marsairforce/ibanez_rg350ex/photos/IMG_4963.jpg

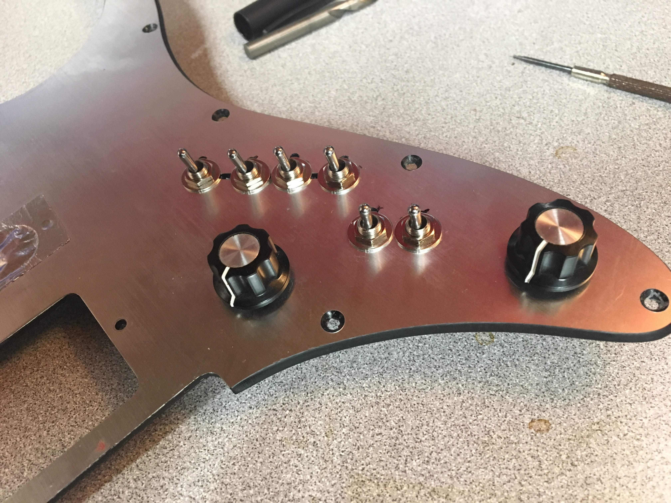
photos/IMG_4963.jpg
