marsairforce/ibanez_rg350ex/photos/IMG_4964.jpg

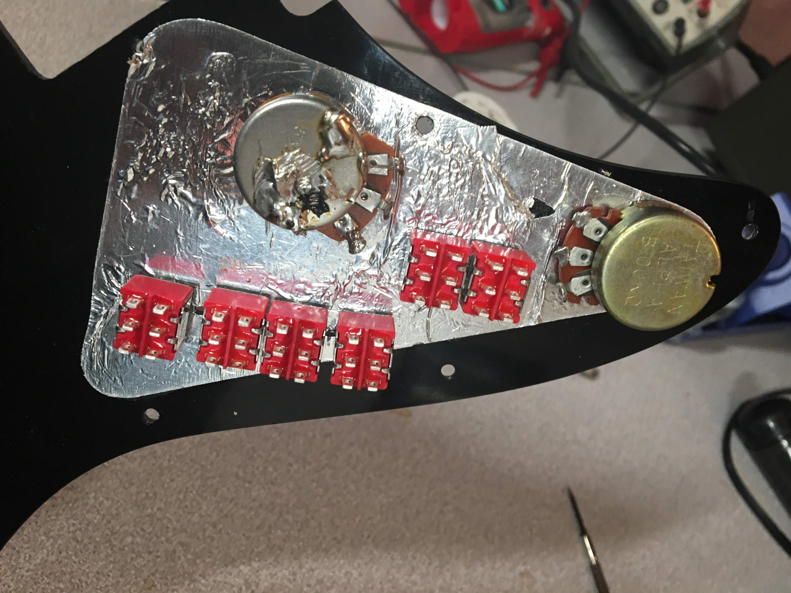
photos/IMG_4964.jpg
