marsairforce/ibanez_rg350ex/photos/IMG_4965.jpg

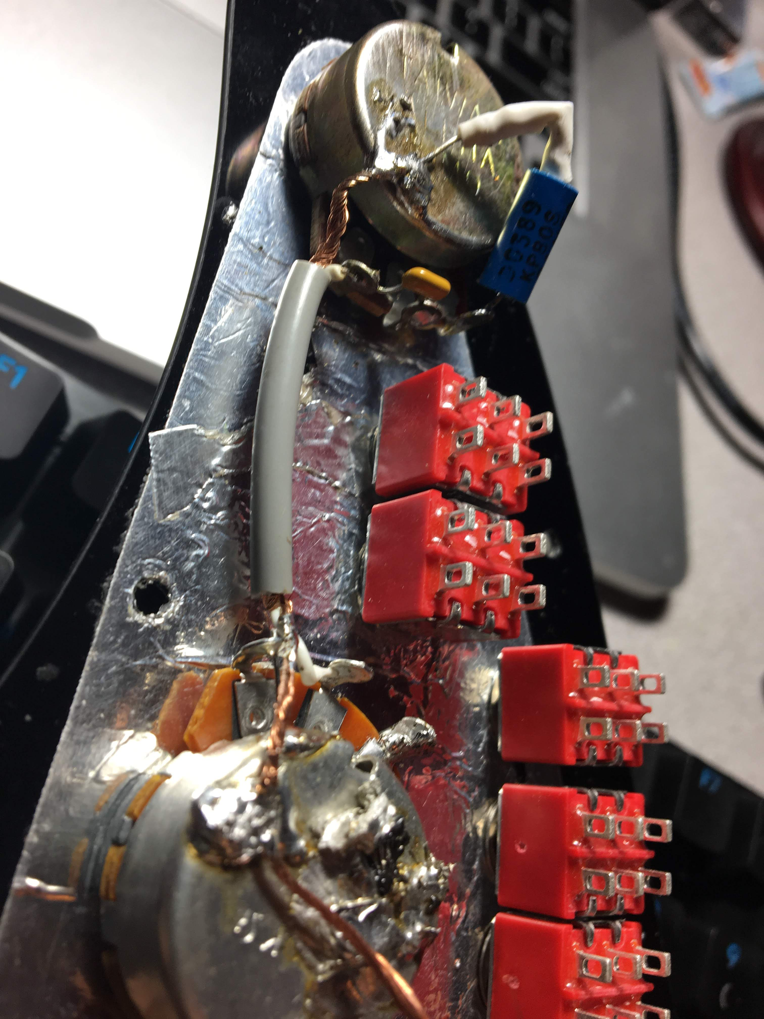
photos/IMG_4965.jpg
