marsairforce/ibanez_rg350ex/photos/IMG_4967.jpg

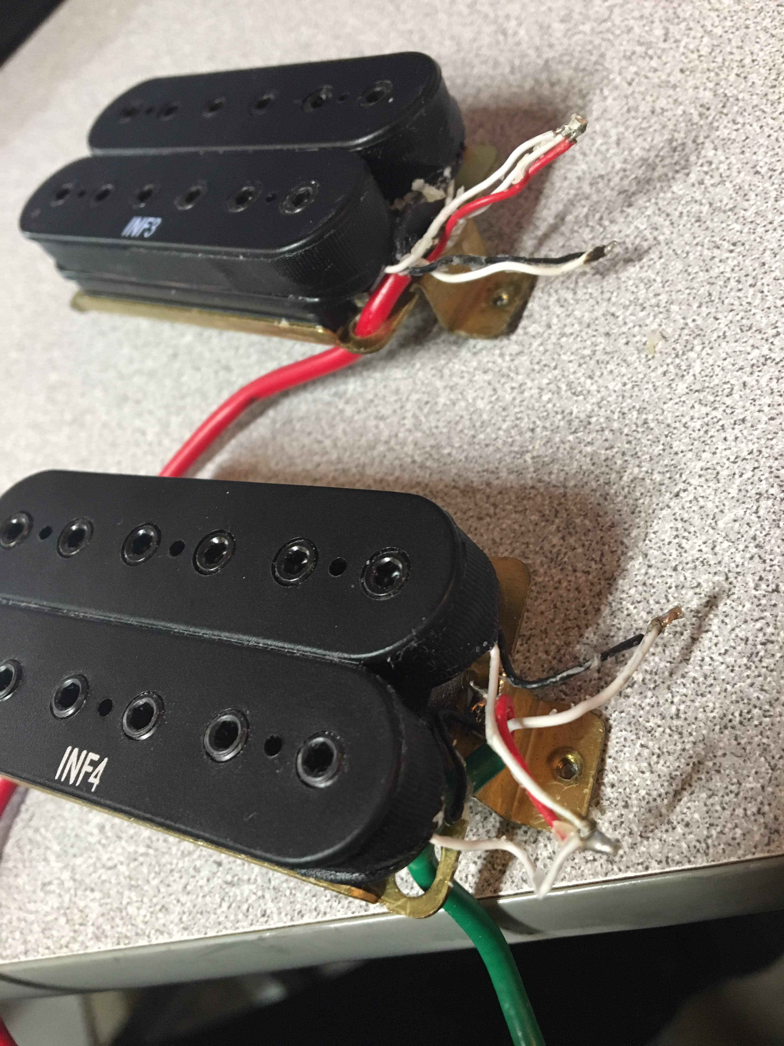
photos/IMG_4967.jpg
