marsairforce/ibanez_rg350ex/photos/IMG_4969.jpg

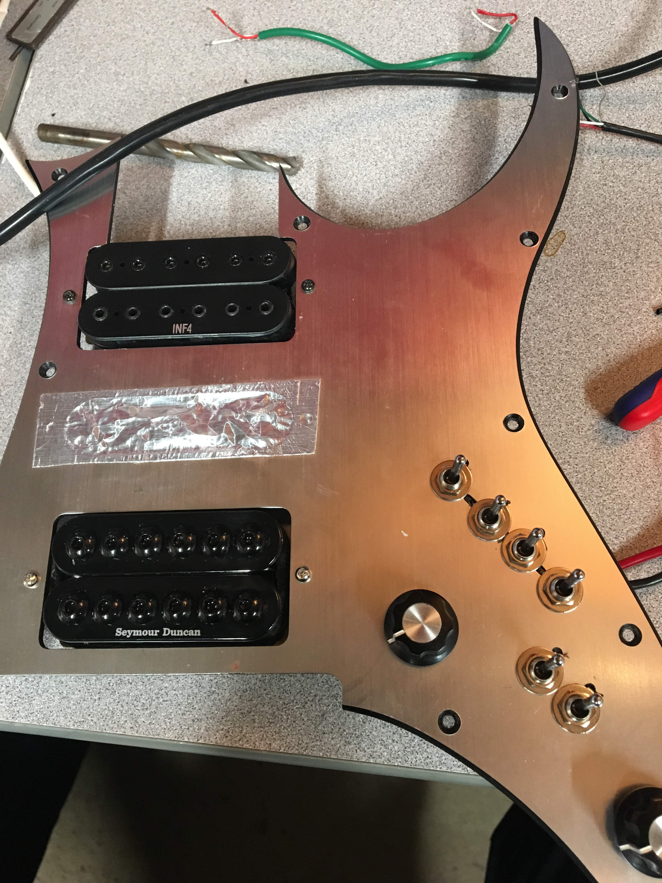
photos/IMG_4969.jpg
