marsairforce/ibanez_rg350ex/photos/IMG_4970.jpg

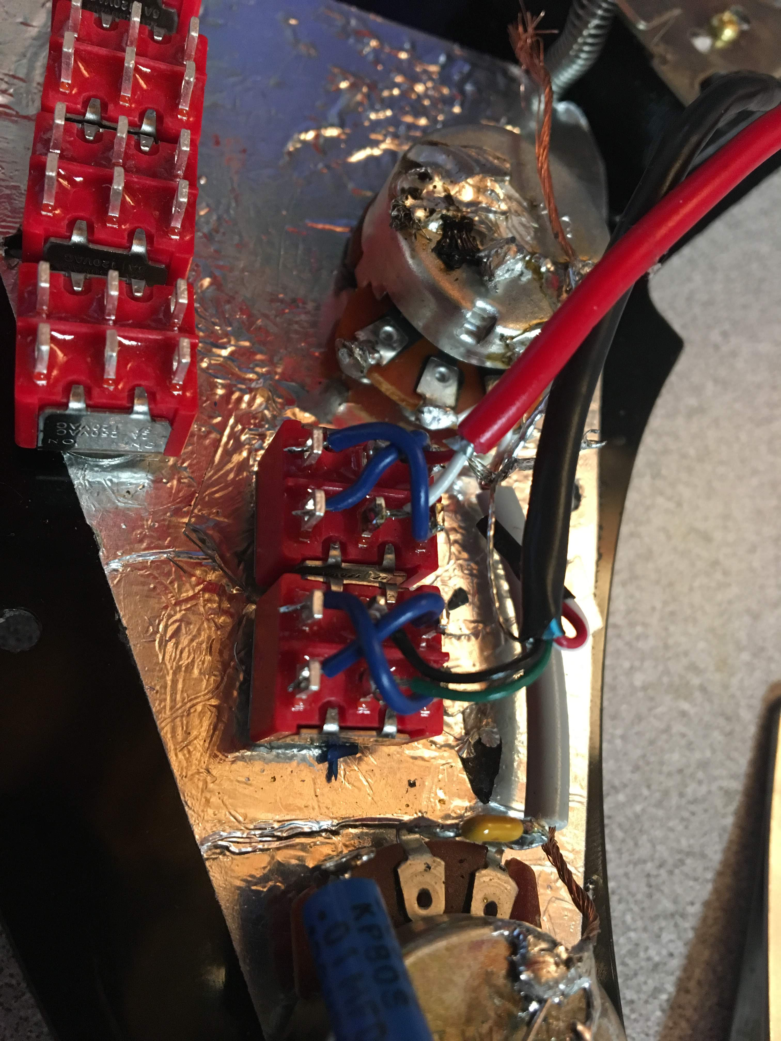
photos/IMG_4970.jpg
