marsairforce/ibanez_rg350ex/photos/IMG_4973.jpg

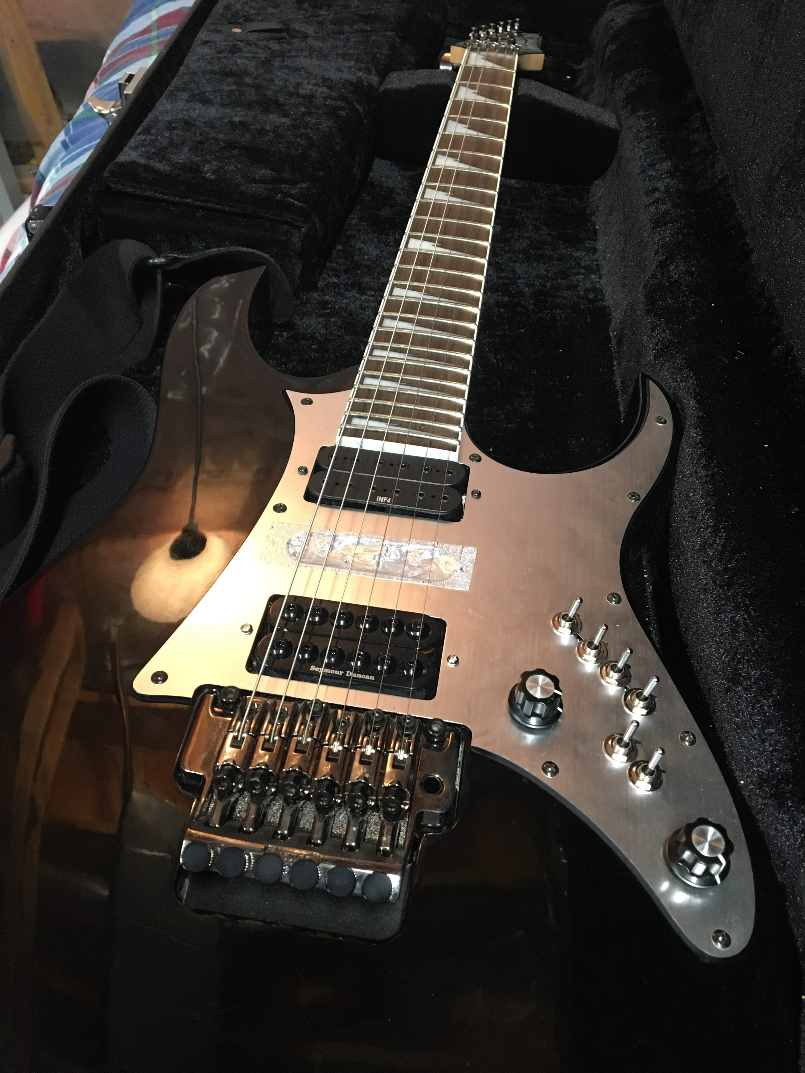
photos/IMG_4973.jpg
