marsairforce/ibanez_rg350ex/photos/IMG_5088.jpg

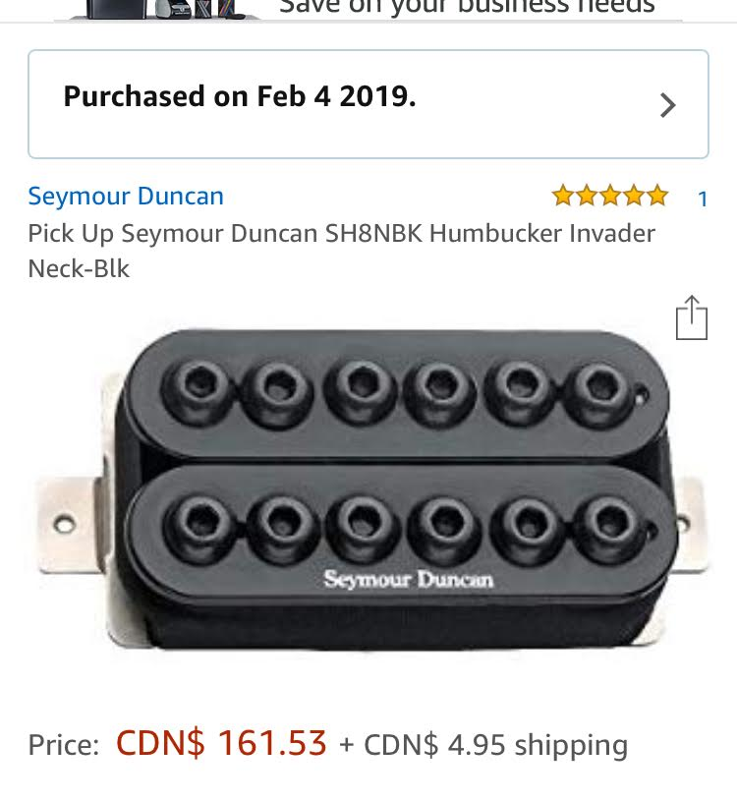
photos/IMG_5088.jpg
