marsairforce/ibanez_rg350ex/photos/IMG_5095.jpg

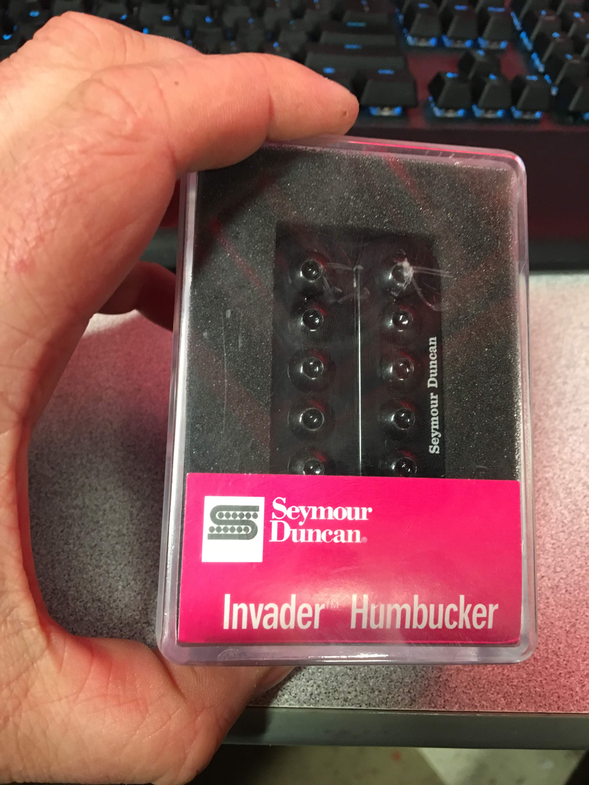
photos/IMG_5095.jpg
