marsairforce/ibanez_rg350ex/photos/IMG_5179.jpg

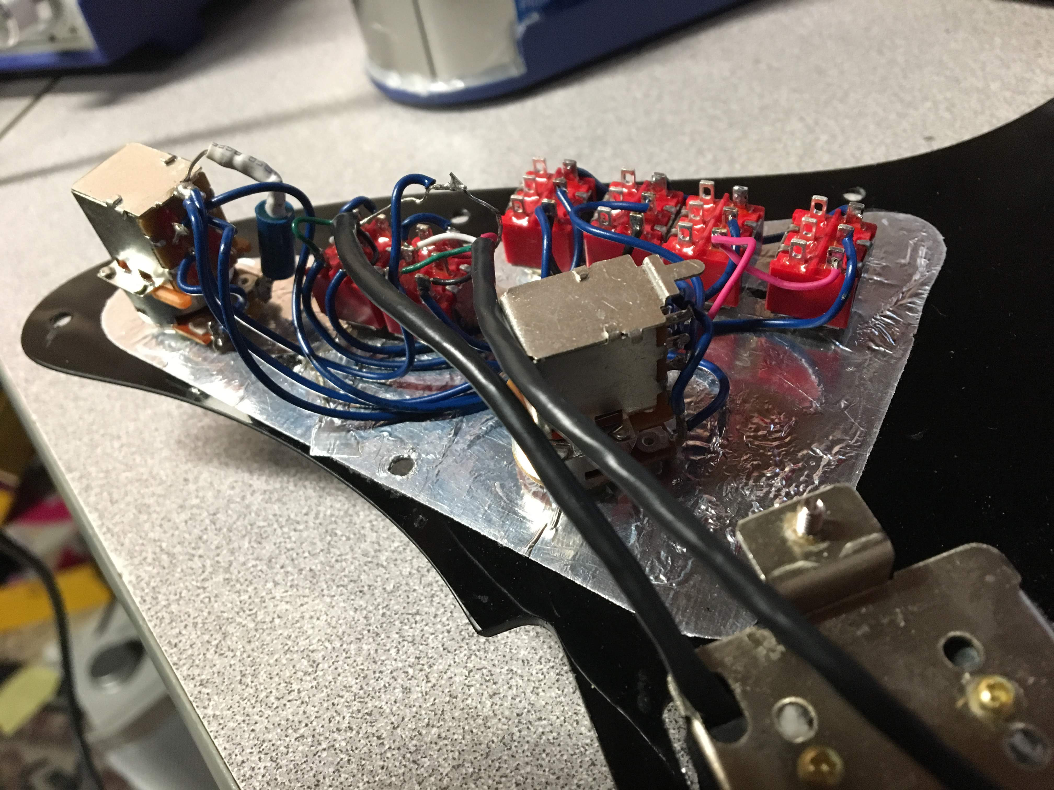
photos/IMG_5179.jpg
