marsairforce/ibanez_rg350ex/photos/IMG_5180.jpg

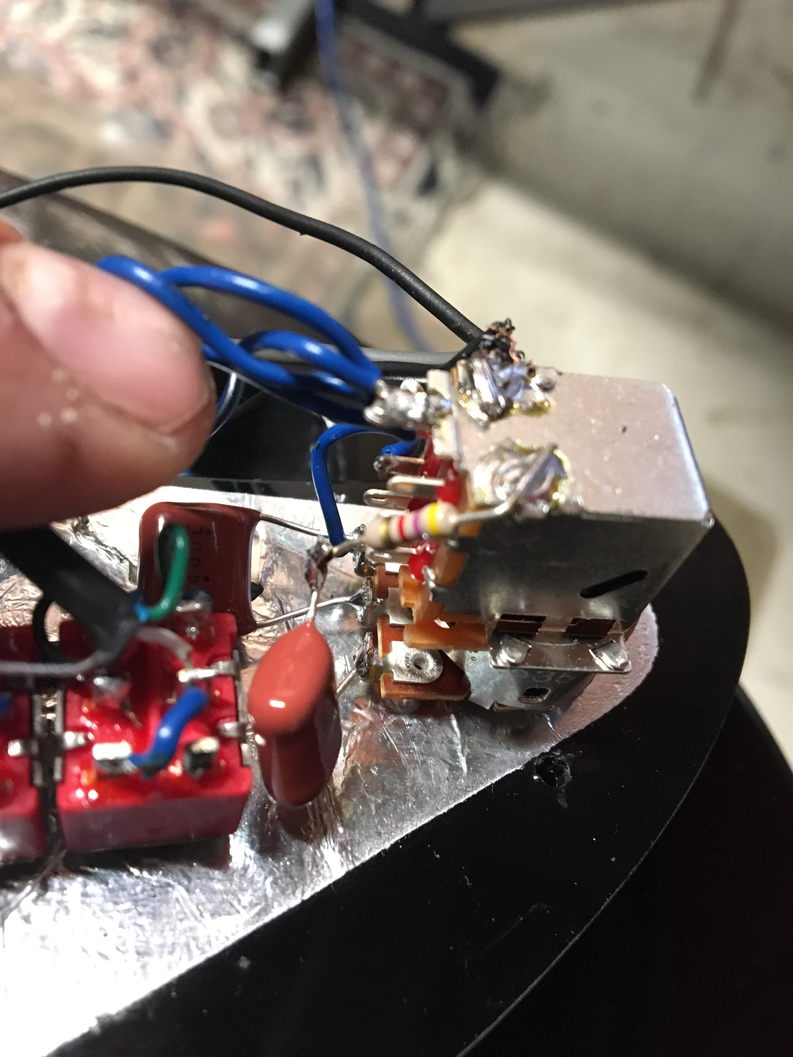
photos/IMG_5180.jpg
