marsairforce/ibanez_rg350ex/photos/IMG_5755.jpg

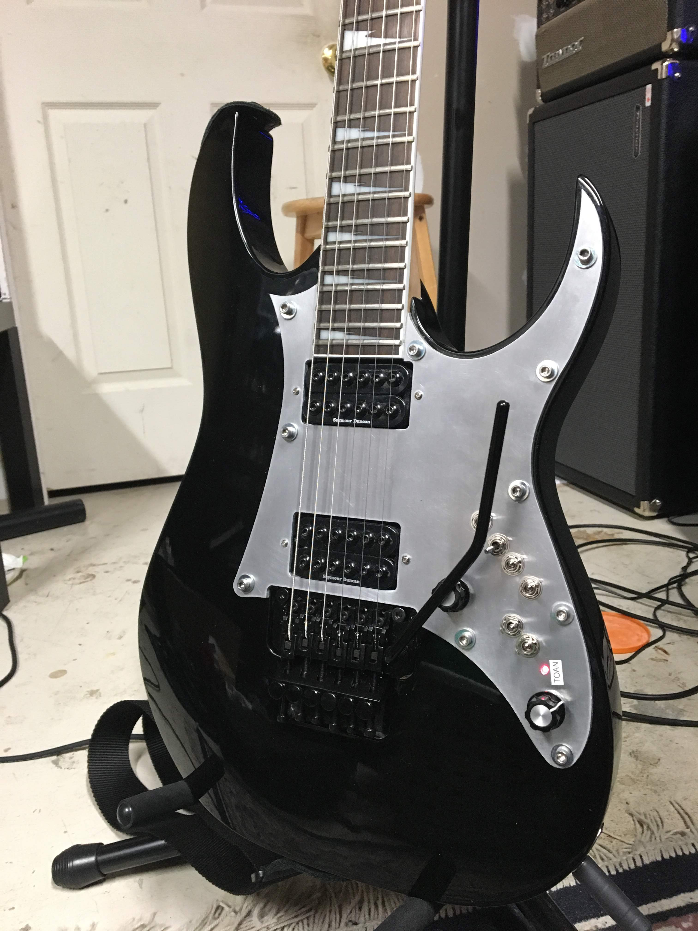
photos/IMG_5755.jpg
